cruzsbrian/aurora/aurora_sw/src/pattern.h

#pragma once

#include <string>
#include <unordered_map>

#include <LuaArduino.h>


using namespace std;


struct Param {
    void *pat;
    string name;
    double min, max, step, val;
};


class Pattern {
public:
    Pattern(int idx, string name, string filename):
        idx(idx), name(name), filename(filename) {
        loaded = false;
        L = NULL;
    }

    void update();
    void load();
    void unload();
    void upload_code(string code);
    void save_code(string code);
    void add_param(const char *name, double min, double max, double step, double val);
    void set_variable(const string &name, double val);

    int idx;
    string name;
    string filename;
    bool loaded;
private:
    void lua_setup();
    string read_from_sd(string filename);
    void write_to_sd(string filename, string data);
    void load_code(string code);

    lua_State *L;
    unordered_map<string, Param> params;
};
